chenjj409/Wireless-Controlling-Smart-Home/image-7.png

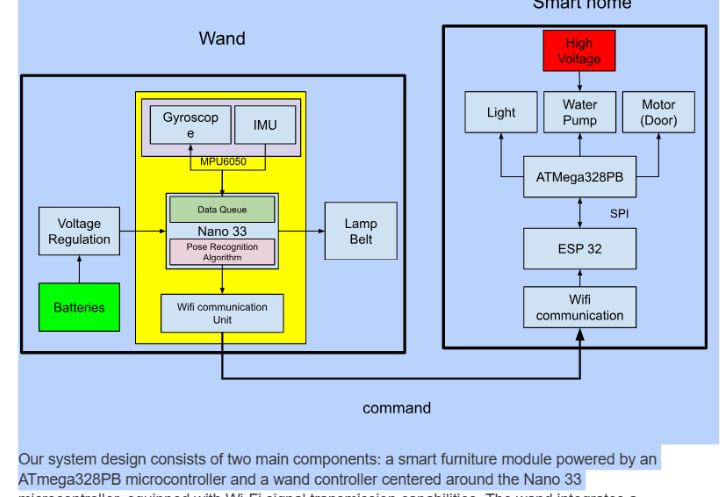
image-7.png
